EERNINUO/ArbWave30/datasheet/AD9767/EVAL-AD9767BOTTOM-web.png

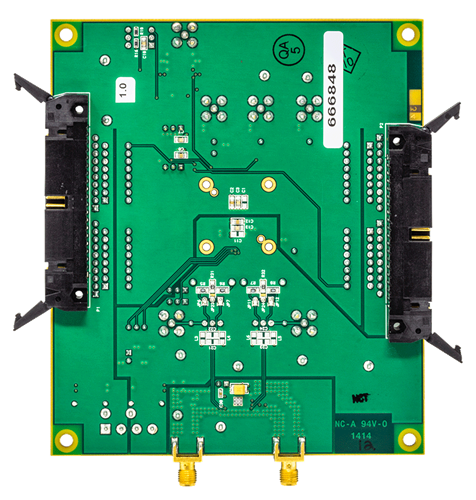
datasheet/AD9767/EVAL-AD9767BOTTOM-web.png
