EERNINUO/ArbWave30/datasheet/AD9767/EVAL-AD9767TOP-web.png

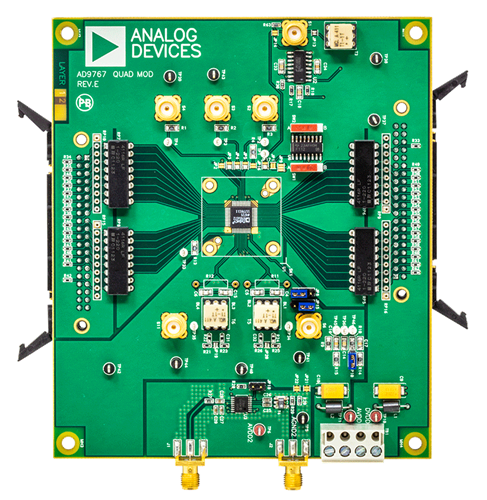
datasheet/AD9767/EVAL-AD9767TOP-web.png
