EERNINUO/ArbWave30/docs/pic/3.3V_D电源.png

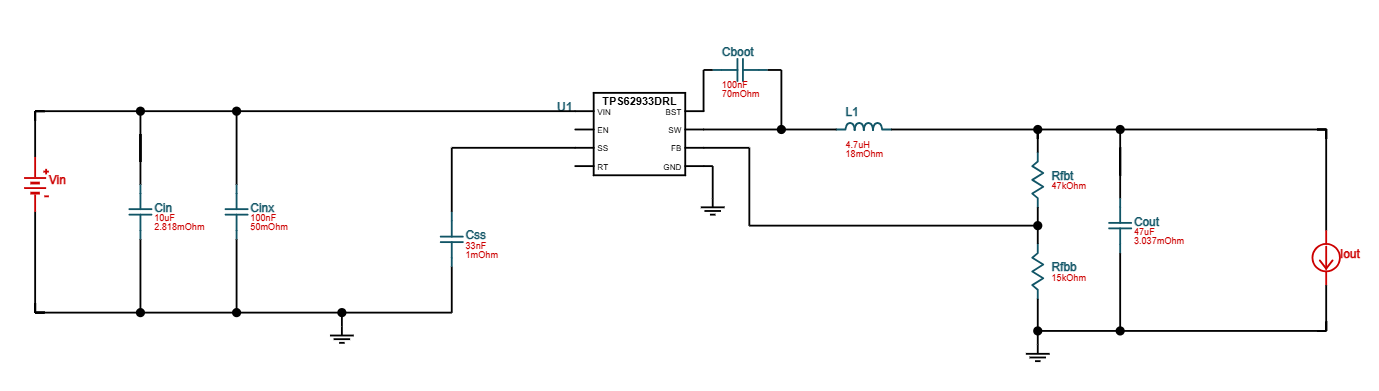
docs/pic/3.3V_D电源.png
