EERNINUO/ArbWave30/docs/pic/差分转单端原理图.png

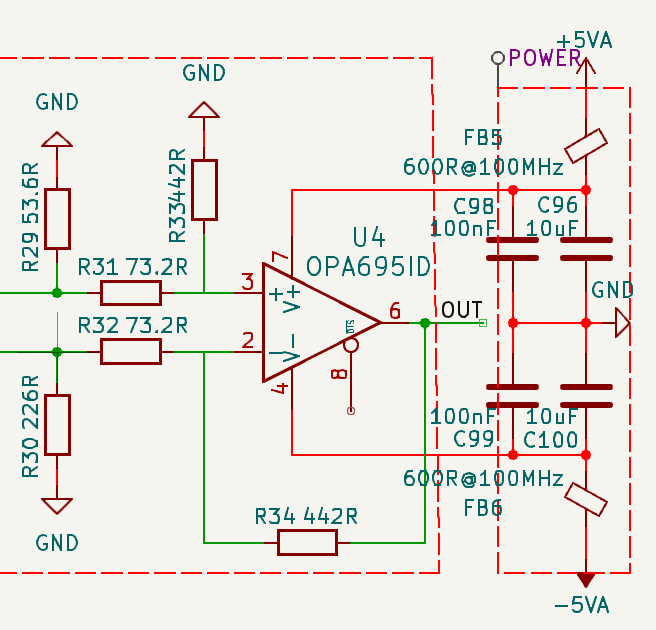
docs/pic/差分转单端原理图.png
