EERNINUO/ArbWave30/docs/pic/控制板电源原理图.png

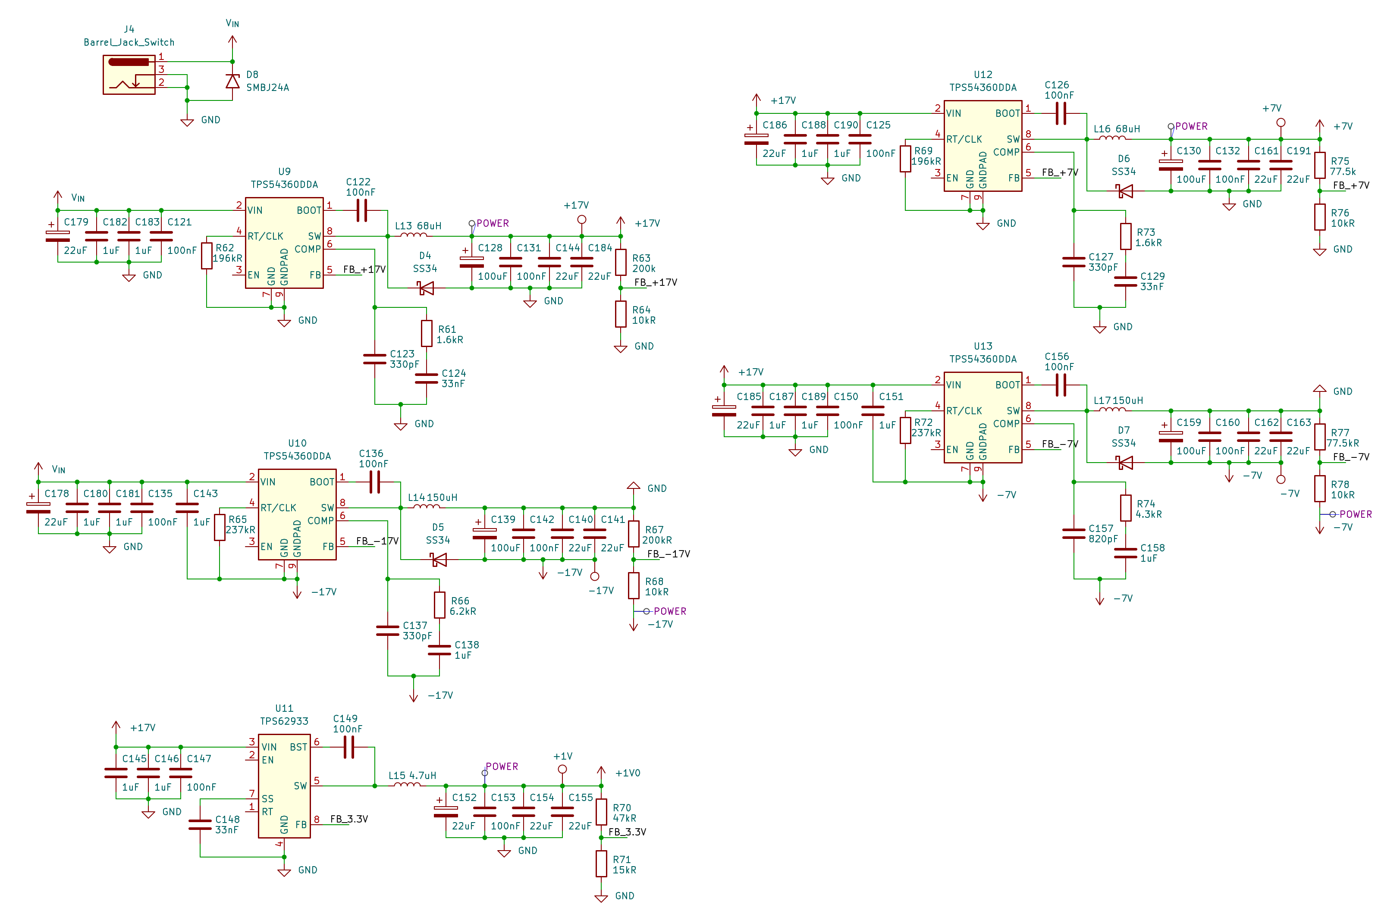
docs/pic/控制板电源原理图.png
