EERNINUO/ArbWave30/scripts/test_diff_to_single/差分转单端幅频特性.png

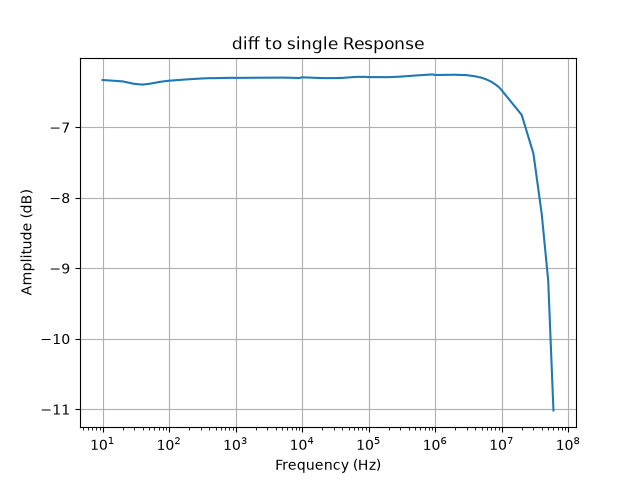
scripts/test_diff_to_single/差分转单端幅频特性.png
