EERNINUO/ArbWave30/firmware/MCU/Application/Core/Inc/main.h

#define SPI1_CS_Pin GPIO_PIN_4
#define SPI1_CS_GPIO_Port GPIOA
#define FPGA_NRST_Pin GPIO_PIN_0
#define FPGA_NRST_GPIO_Port GPIOB
#define FPGA_INT_Pin GPIO_PIN_1
#define FPGA_INT_GPIO_Port GPIOB
#define GPIO2_Pin GPIO_PIN_2
#define GPIO2_GPIO_Port GPIOB
#define Debug_LED_Pin GPIO_PIN_14
#define Debug_LED_GPIO_Port GPIOB
#define Buzzer_Pin GPIO_PIN_15
#define Buzzer_GPIO_Port GPIOB
#define VBUS_Check_Pin GPIO_PIN_10
#define VBUS_Check_GPIO_Port GPIOA
#define ROM_WP_Pin GPIO_PIN_5
#define ROM_WP_GPIO_Port GPIOB
#define VBUS_EVENT_FLAG   (1UL << 0)
