EERNINUO/ArbWave30/firmware/FPGA/Application/src/dac_interface/fifo_hs/fifo_hs.v

//
//Written by GowinSynthesis
//Tool Version "V1.9.12.01 (64-bit)"
//IP Version: 1.0
//Wed Jul 22 23:22:53 2026

//Source file index table:
//file0 "\E:/Gowin/Gowin_V1.9.12.01_x64/IDE/ipcore/FIFO_HS/data/fifo_hs.v"
//file1 "\E:/Gowin/Gowin_V1.9.12.01_x64/IDE/ipcore/FIFO_HS/data/fifo_hs_top.v"
`timescale 100 ps/100 ps
`pragma protect begin_protected
`pragma protect version="2.3"
`pragma protect author="default"
`pragma protect author_info="default"
`pragma protect encrypt_agent="GOWIN"
`pragma protect encrypt_agent_info="GOWIN Encrypt Version 2.3"

`pragma protect encoding=(enctype="base64", line_length=76, bytes=256)
`pragma protect key_keyowner="GOWIN",key_keyname="GWK2023-09",key_method="rsa"
`pragma protect key_block
hvyrXGPbFZGhTykb3xYgOSOJC/8g/gi7LYrOf05b09vDxATHhndsXuijwsCOMQgbYqsIgHP3RnEM
Rw0rY+Tx68k8GA944iFXXuVmDuZVxvzm3dxJ/MQpGk6gwrDFW/wiN1i7vKhTapiXc+ZVs4z9glZ/
BGb9DVxE7R0pBb6QXPoxQl8V5ILhsJ/TnIsJKtgFHPuZHJoefHJqqtJMOFz5XfhmhEZ/7+cq03Up
PvAxiyRcwaX5Kw6oyLntS5oKswImobAMli/tsCWQMh+AXQr+b8OssE1WJE50jWsgjSeoUzPvudMn
TLqqv0Tg+eiNC3b3N8/OuCoQIwIugXn4LpNDag==

`pragma protect encoding=(enctype="base64", line_length=76, bytes=12720)
`pragma protect data_keyowner="default-ip-vendor"
`pragma protect data_keyname="default-ip-key"
`pragma protect data_method="aes128-cfb"
`pragma protect data_block
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
Yj7KdwXbLTUg
`pragma protect end_protected
module FIFO_HS_Top (
  Data,
  WrClk,
  RdClk,
  WrEn,
  RdEn,
  Q,
  Empty,
  Full
)
;
input [15:0] Data;
input WrClk;
input RdClk;
input WrEn;
input RdEn;
output [15:0] Q;
output Empty;
output Full;
wire VCC;
wire GND;
  \~fifo.FIFO_HS_Top  fifo_inst (
    .RdClk(RdClk),
    .WrClk(WrClk),
    .WrEn(WrEn),
    .RdEn(RdEn),
    .Data(Data[15:0]),
    .Empty(Empty),
    .Full(Full),
    .Q(Q[15:0])
);
  VCC VCC_cZ (
    .V(VCC)
);
  GND GND_cZ (
    .G(GND)
);
  GSR GSR (
    .GSRI(VCC) 
);
endmodule /* FIFO_HS_Top */
