EERNINUO/ArbWave30/firmware/FPGA/Application/src/dac_interface/dac_interface.v

/*
 * SPDX-License-Identifier: GPL-3.0-only
 * Copyright (C) 2026 [EERNINUO]
 *
 * [This file is part of ArbWave30.]
 *
 * ArbWave30 is free software: you can redistribute it and/or modify
 * it under the terms of the GNU General Public License as published by
 * the Free Software Foundation, version 3 of the License.
 * ...
 */

module dac_interface #(
	parameter SYS_CLK_FREQ = 150_000_000
)(
	// 系统接口
    input  wire        sys_clk,
	input  wire        data_clk,
    input  wire        sys_rst_n,

	// DAC 数据接口
    input  wire [15:0] ch1_data_in,
    output reg  [15:0] ch1_data_out,

	// DAC 控制接口
	output reg        rst_p,
	output wire        cs,
	output wire        clk,
	output wire        mosi,
	input 			   miso
);

wire [15:0] ch1_fifo_out;

FIFO_HS_Top u_FIFO_HS_Top(
	.Data(-ch1_data_in), //input [15:0] Data，因为 CH1 外部电路反向连接，所以输入数据取反
	.WrClk(sys_clk), //input WrClk
	.RdClk(data_clk), //input RdClk
	.WrEn(sys_rst_n), //input WrEn
	.RdEn(sys_rst_n), //input RdEn
	.Q(ch1_fifo_out), //output [15:0] Q
	.Empty(), //output Empty
	.Full() //output Full
);

always @(posedge data_clk or negedge sys_rst_n) begin
    if (!sys_rst_n)
        ch1_data_out <= 16'd0;
    else
        ch1_data_out <= ch1_fifo_out; // 用 DCO 时钟打一拍
end

SPI_master #(
	.SYS_CLK_FREQ 	(150_000_000)
) u_SPI_master (
	.sys_clk   	(sys_clk    ),
	.sys_rst_n 	(sys_rst_n  ),
	.cs        	(cs         ),
	.clk       	(clk        ),
	.mosi      	(mosi       ),
	.miso      	(miso       ),
	.send_data 	(8'h00      ),
	.start     	(1'd0),
	.rece_data 	(),
	.busy      	()
);

// DAC 复位信号
always @(posedge sys_clk or negedge sys_rst_n) begin
	if(!sys_rst_n) begin
		rst_p <= 1'b1;
	end else begin
		rst_p <= 1'b0;
	end
end

endmodule
