EERNINUO/ArbWave30/firmware/FPGA/Application/src/dac_interface/fifo_hs/fifo_hs_tmp.v

//Copyright (C)2014-2025 Gowin Semiconductor Corporation.
//All rights reserved.
//File Title: Template file for instantiation
//Tool Version: V1.9.12.01 (64-bit)
//IP Version: 1.0
//Part Number: GW2AR-LV18EQ144C8/I7
//Device: GW2AR-18
//Device Version: C
//Created Time: Wed Jul 22 23:22:53 2026

//Change the instance name and port connections to the signal names
//--------Copy here to design--------

	FIFO_HS_Top your_instance_name(
		.Data(Data), //input [15:0] Data
		.WrClk(WrClk), //input WrClk
		.RdClk(RdClk), //input RdClk
		.WrEn(WrEn), //input WrEn
		.RdEn(RdEn), //input RdEn
		.Q(Q), //output [15:0] Q
		.Empty(Empty), //output Empty
		.Full(Full) //output Full
	);

//--------Copy end-------------------
