EERNINUO/ArbWave30/firmware/FPGA/Application/src/wave_generation/dds_ii/dds_ii_tmp.v

//Copyright (C)2014-2025 Gowin Semiconductor Corporation.
//All rights reserved.
//File Title: Template file for instantiation
//Tool Version: V1.9.12.01 (64-bit)
//IP Version: 1.1
//Part Number: GW2AR-LV18EQ144C8/I7
//Device: GW2AR-18
//Device Version: C
//Created Time: Fri Jul  3 14:16:33 2026

//Change the instance name and port connections to the signal names
//--------Copy here to design--------

	DDS_II_Top your_instance_name(
		.clk_i(clk_i), //input clk_i
		.rst_n_i(rst_n_i), //input rst_n_i
		.phase_valid_i(phase_valid_i), //input phase_valid_i
		.phase_inc_i(phase_inc_i), //input [47:0] phase_inc_i
		.phase_off_i(phase_off_i), //input [47:0] phase_off_i
		.phase_out_o(phase_out_o), //output [47:0] phase_out_o
		.sine_o(sine_o), //output [15:0] sine_o
		.data_valid_o(data_valid_o) //output data_valid_o
	);

//--------Copy end-------------------
