EERNINUO/ArbWave30/firmware/Clock_Generator_Config/MCU_Project/Core/Inc/Clock_Generator_Config.h

#ifndef __CLOCK_GENERATOR_CONFIG_H__
#define __CLOCK_GENERATOR_CONFIG_H__

#include "stm32f4xx_hal.h"

#define CDCI6214_I2C_ADDR  0x74

// 寄存器地址与值配对结构
typedef struct {
    uint16_t addr;
    uint16_t value;
} reg_cfg_t;

// 按地址降序排列的寄存器配置表 (从 R70 到 R0)
static const reg_cfg_t cdci6214_regs[] = {
    {0x44, 0x0000},  // R68
    {0x43, 0x2000},  // R67
    {0x42, 0x0002},  // R66
    {0x41, 0x340F},  // R65
    {0x40, 0x0D00},  // R64
    {0x3F, 0x1002},  // R63
    {0x3E, 0x0942},  // R62
    {0x3D, 0x0015},  // R61
    {0x3C, 0x1800},  // R60
    {0x3B, 0x2F10},  // R59
    {0x3A, 0x0800},  // R58
    {0x39, 0x650A},  // R57
    {0x38, 0x0104},  // R56
    {0x37, 0x0400},  // R55
    {0x36, 0x0000},  // R54
    {0x35, 0x0080},  // R53
    {0x34, 0x0800},  // R52
    {0x33, 0x650A},  // R51
    {0x32, 0x0104},  // R50
    {0x31, 0x0000},  // R49
    {0x30, 0x0000},  // R48
    {0x2F, 0x0080},  // R47
    {0x2E, 0x0800},  // R46
    {0x2D, 0x650A},  // R45
    {0x2C, 0x0500},  // R44
    {0x2B, 0x0C00},  // R43
    {0x2A, 0x0000},  // R42
    {0x29, 0x0080},  // R41
    {0x28, 0x0800},  // R40
    {0x27, 0x650A},  // R39
    {0x26, 0x0500},  // R38
    {0x25, 0x0400},  // R37
    {0x24, 0x0000},  // R36
    {0x23, 0x0080},  // R35
    {0x22, 0x5000},  // R34
    {0x21, 0x0700},  // R33
    {0x20, 0x0000},  // R32
    {0x1F, 0x721E},  // R31
    {0x1E, 0x4051},  // R30
    {0x1D, 0x1E00},  // R29
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
};

HAL_StatusTypeDef CDCI6214_WriteConfig(I2C_HandleTypeDef *hi2c, uint8_t dev_addr);


#endif /* __CLOCK_GENERATOR_CONFIG_H__ */
